AlfredWilmot/HydrogelHeater/circuit_sims/H_bridge_experimentation.asc

C1: cap; 100n
C2: cap; 100n
C3: cap; 100n
L1: ind; 10µH
M1: pmos; AO6407
M2: nmos; AO6408
M3: nmos; AO6408
M4: pmos; AO6407
M5: nmos; AO6408
Q1: npn; 2N2222
Q2: pnp; 2N2907
Q3: npn; 2N2222
R1: res; 4.7k
R2: res; 4.7k
R3: res; 4.7k
R4: res; 10k
R5: res; 0.5
R6: res; 10k
R7: res; 1k
R8: res; 1k
R9: res; 100
R10: res; 10
R11: res; 1
R15: res; 10k
R16: res; 10k
U1: LT1014
U2: LT1014
U4: OP747
V1: voltage; PULSE(0 5 10ms 10n 10n 0.9m 1ms)
V2: voltage; 10
V3: voltage; 5
V5: voltage; 5
Named nets: 0, pwm, V2, V_out, V3
.tran 100ms
