AlfredWilmot/HydrogelHeater/circuit_sims/Draft1.asc

C1: cap; 100n
C2: cap; 100n
C3: cap; 100n
R1: res; 0.1
R2: res; 1
R3: res; 10k
R4: res; 10k
R5: res; 10k
U1: tip120
U2: OP747
V1: voltage; 5
V2: voltage; 10
V3: voltage; PULSE(0 5 10ms 10ns 10ns 0.8ms 1ms)
Named nets: 0, V_out, pwm
.tran 100ms
