AlfredWilmot/HydrogelHeater/circuit_sims/Draft3.asc

C1: cap; 100nF
C2: cap; 100nF
C3: cap; 100nF
C4: cap; 100nF
C5: cap; 100nF
C6: cap; 100nF
M1: nmos; IRF6620
M2: nmos; IRF6620
R1: res; 100k
R2: res; 100k
R3: res; 1000k
R4: res; 50k
R5: res; 100k
R6: res; 100k
R7: res; 1000k
R8: res; 50k
R9: res; 190k
R10: res; 560
R11: res; 0.1
R12: res; 10k
R13: res; 15k
R14: res; 15k
R15: res; 10k
R16: res; 1000k
R17: res; 100k
R18: res; 100k
R19: res; 100k
R20: res; 100k
R21: res; 560
R22: res; 0.1
R23: res; 15k
R24: res; 190k
R25: res; 10k
R26: res; 15k
R27: res; 10k
R28: res; 1000k
U1: uA741
U2: uA741
U3: uA741
U4: uA741
U5: uA741
U6: uA741
V1: voltage; PULSE(0 3.3 5ms 10ns 10ns 0.1s 1ms)
V2: voltage; 3.3
V3: voltage; 5
Named nets: 0, pwm_in, 3V3, pwm, !pwm, PWR, load_side, shunt_side
.tran 0 0.2s 0 1ms
Inverting and non-inverting schmitt triggers 
(so two PWM signals are as complimentary as possible).
 
Schmitt trigger design taken from here: 
https://www.circuitstoday.com/schmitt-trigger-using-op-amp
3.3V supply, and a single PWM signal from an MCU
